gowenrw/84_Badge/art/inspiration/LSF01.jpg

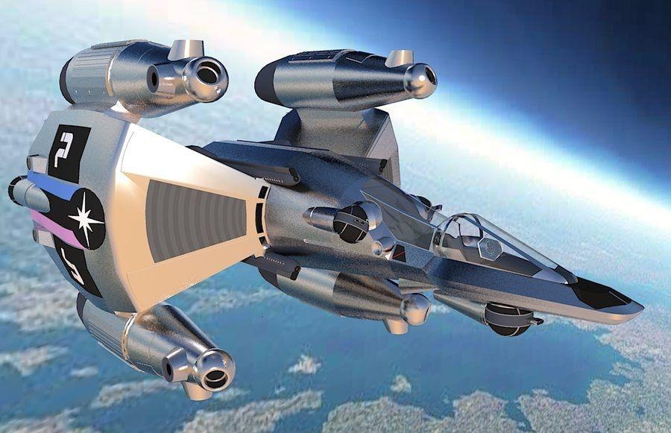
art/inspiration/LSF01.jpg
