gowenrw/84_Badge/art/inspiration/LSF02.jpg

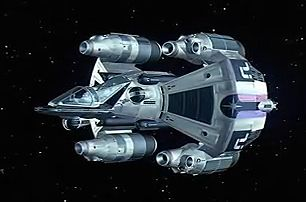
art/inspiration/LSF02.jpg
