gowenrw/84_Badge/art/inspiration/LSF03.png

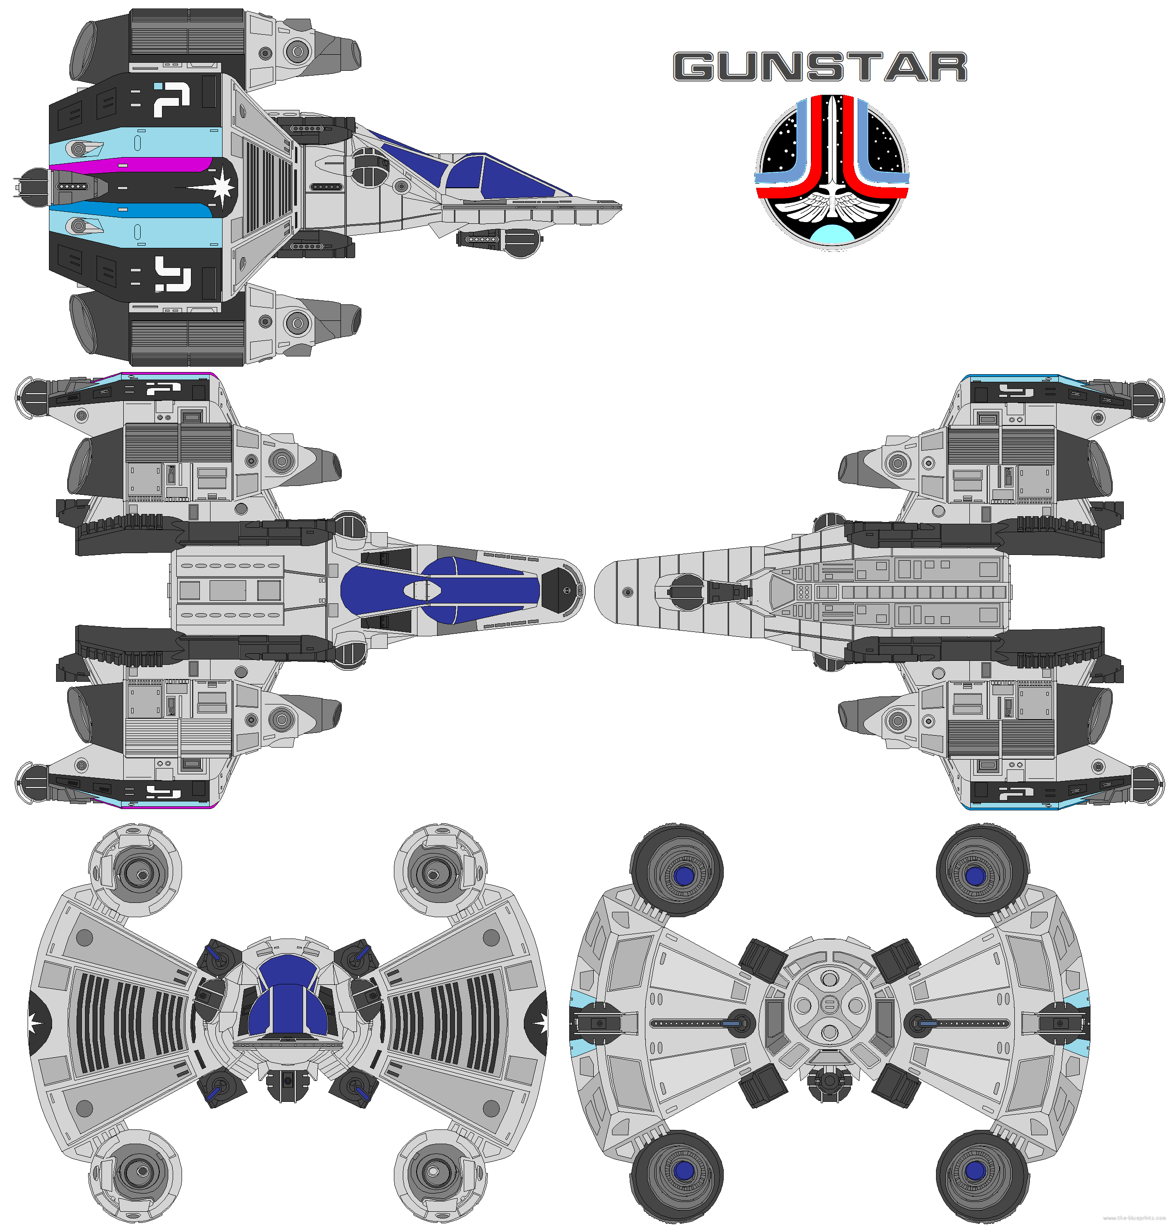
art/inspiration/LSF03.png
