gowenrw/84_Badge/art/inspiration/LSF04.jpg

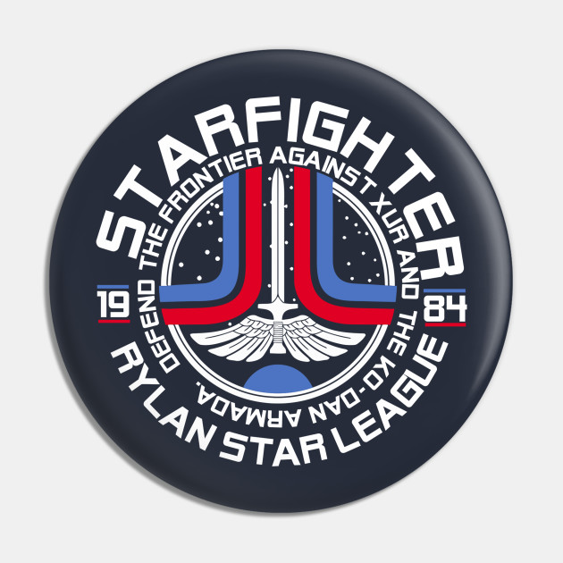
art/inspiration/LSF04.jpg
