gowenrw/84_Badge/art/inspiration/LSF05.jpg

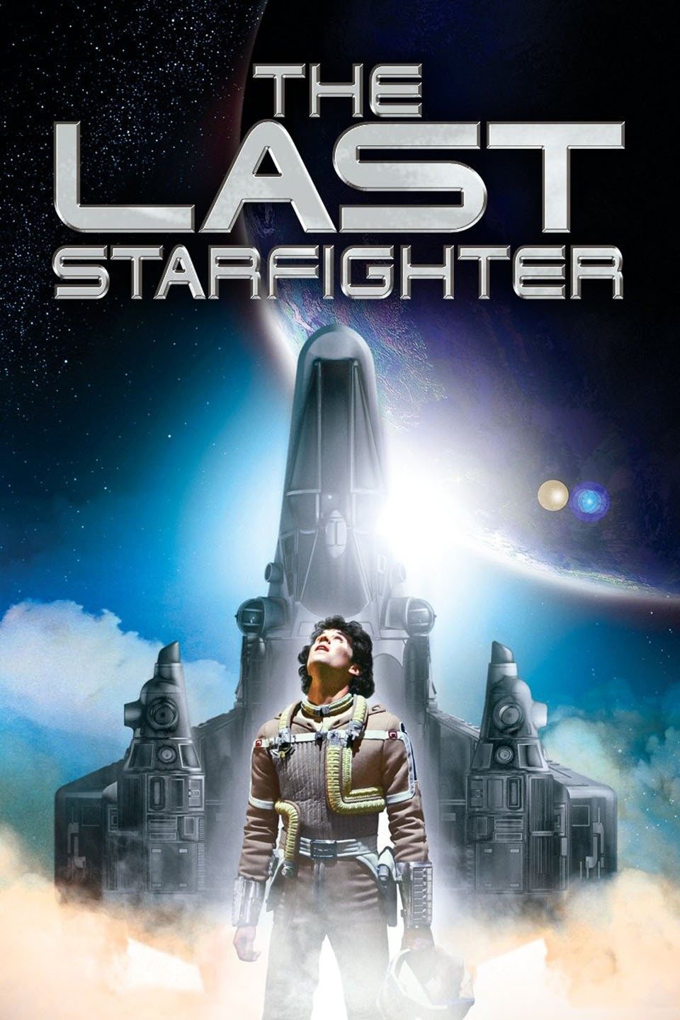
art/inspiration/LSF05.jpg
