gowenrw/84_Badge/art/inspiration/Orwell01.jpg

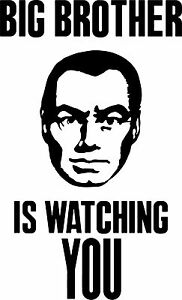
art/inspiration/Orwell01.jpg
