gowenrw/84_Badge/art/inspiration/Orwell02.jpg

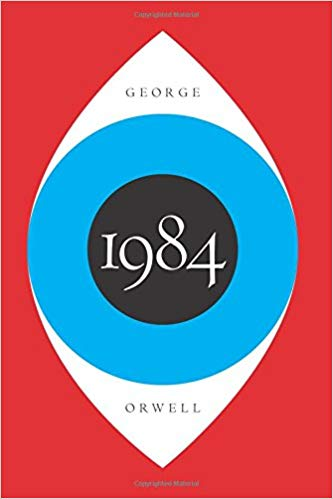
art/inspiration/Orwell02.jpg
