gowenrw/84_Badge/art/inspiration/Orwell03.jpg

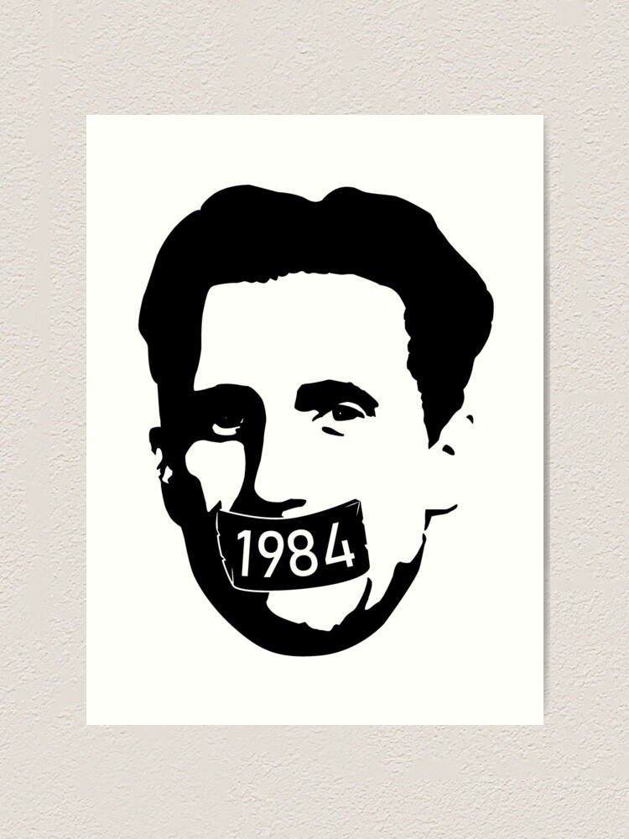
art/inspiration/Orwell03.jpg
