gowenrw/84_Badge/art/inspiration/Orwell04.png

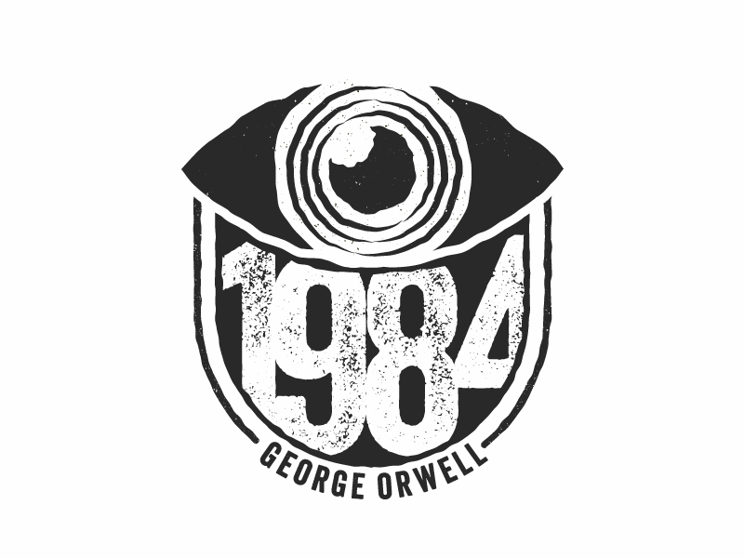
art/inspiration/Orwell04.png
