gowenrw/84_Badge/art/inspiration/Term01.jpg

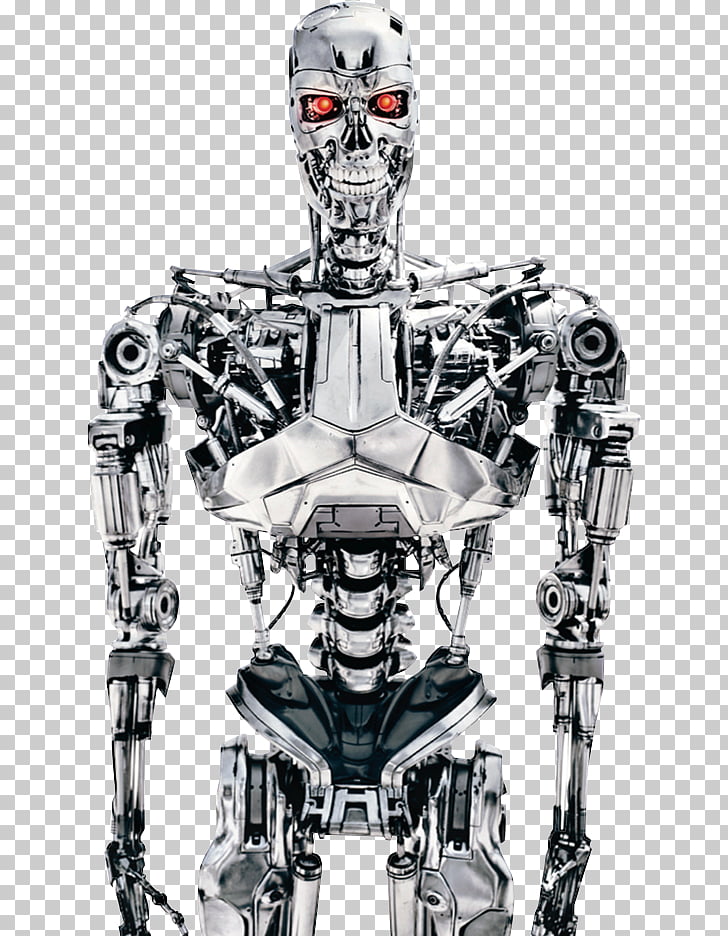
art/inspiration/Term01.jpg
