gowenrw/84_Badge/art/inspiration/Term02.jpg

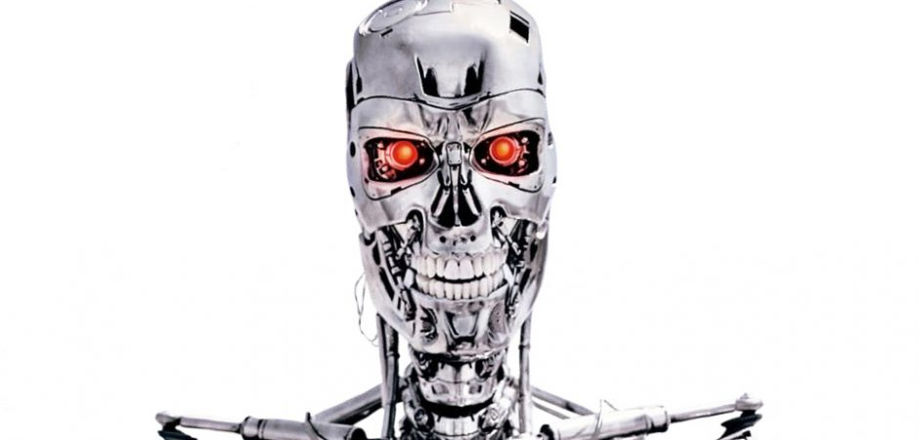
art/inspiration/Term02.jpg
