gowenrw/84_Badge/art/inspiration/Term03.jpg

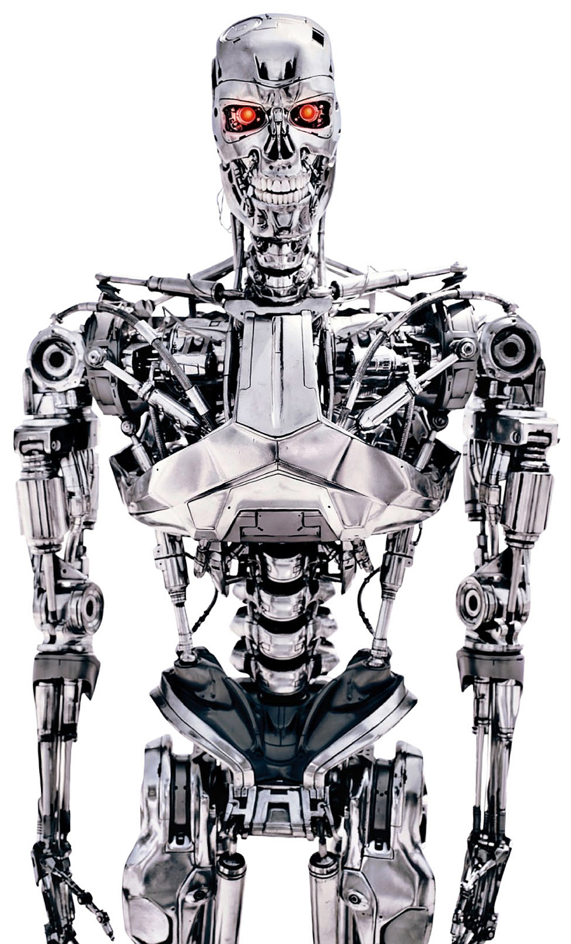
art/inspiration/Term03.jpg
