gowenrw/84_Badge/art/inspiration/Term04.jpg

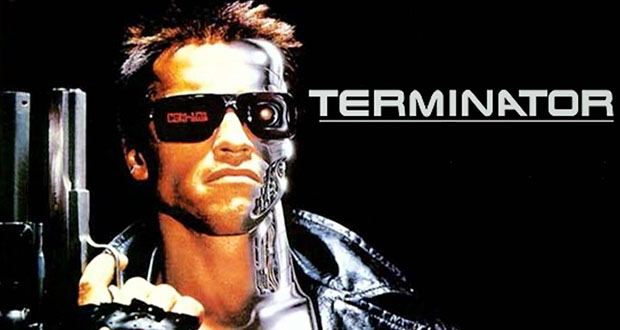
art/inspiration/Term04.jpg
