gowenrw/84_Badge/art/inspiration/Term05.jpg

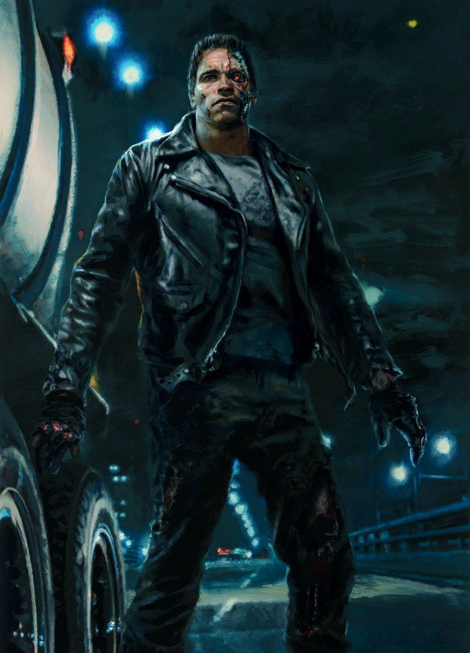
art/inspiration/Term05.jpg
