gowenrw/84_Badge/art/inspiration/WW01.jpg

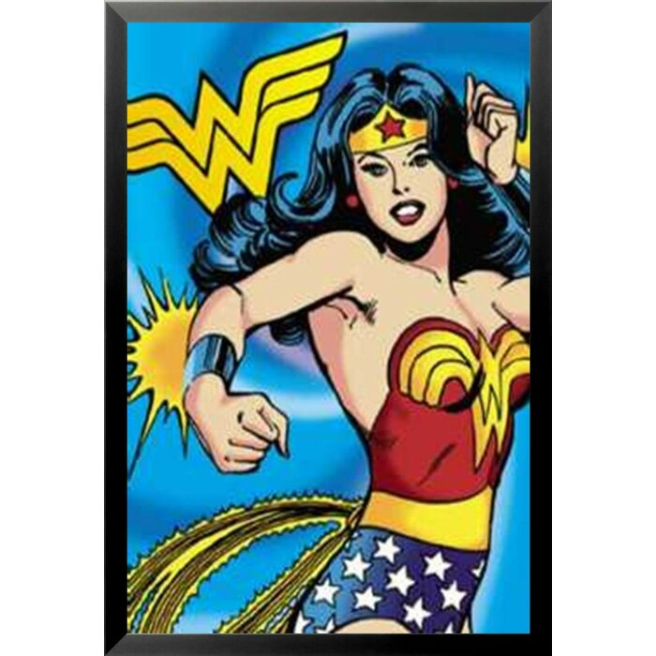
art/inspiration/WW01.jpg
