gowenrw/84_Badge/art/inspiration/WW02.jpg

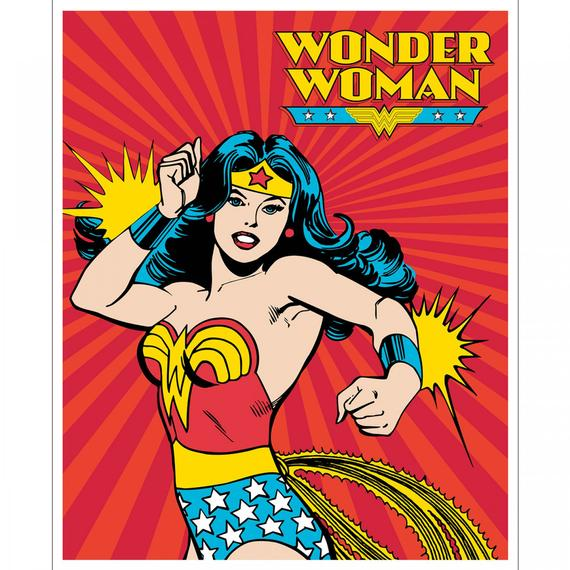
art/inspiration/WW02.jpg
