gowenrw/84_Badge/art/inspiration/WW03.jpg

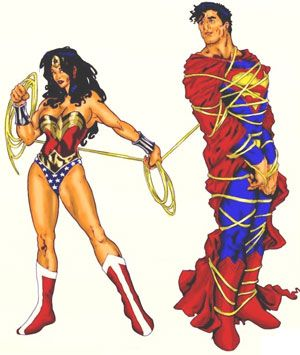
art/inspiration/WW03.jpg
