gowenrw/84_Badge/art/inspiration/WW04.jpg

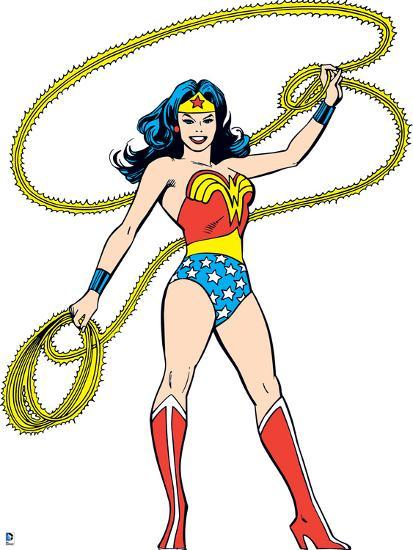
art/inspiration/WW04.jpg
