gowenrw/84_Badge/art/inspiration/WW05.jpg

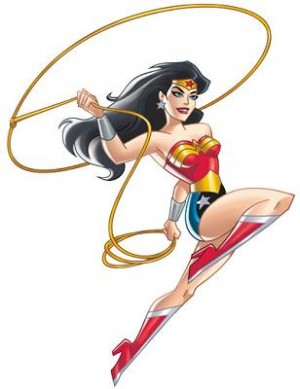
art/inspiration/WW05.jpg
