gowenrw/84_Badge/eda/prod/3d_models/TS2306A.step

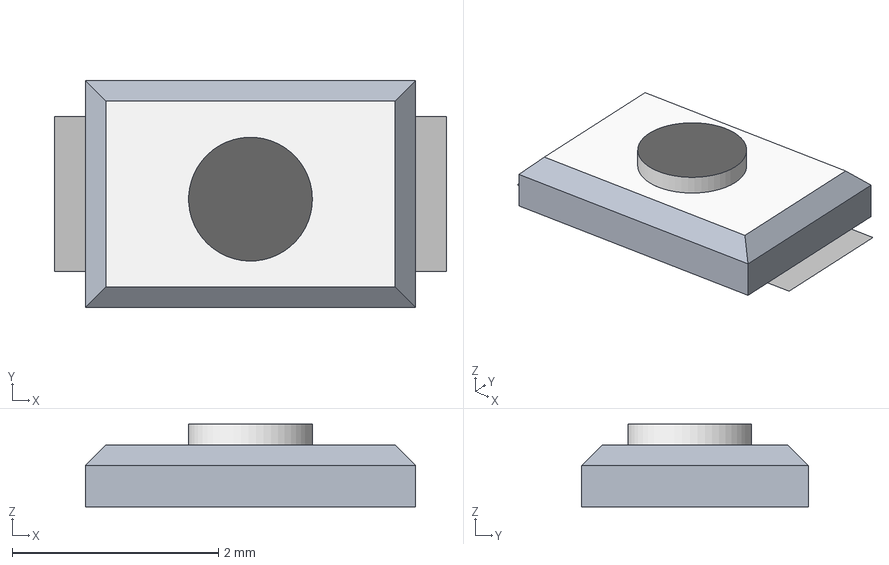
[picture p69: CAD file, 2020-01-20]
eda/prod/3d_models/TS2306A.step
3.80 x 2.20 x 0.8 mm
Plane
