gowenrw/84_Badge/eda/dev/3d_models/C_1206_3216Metric.step

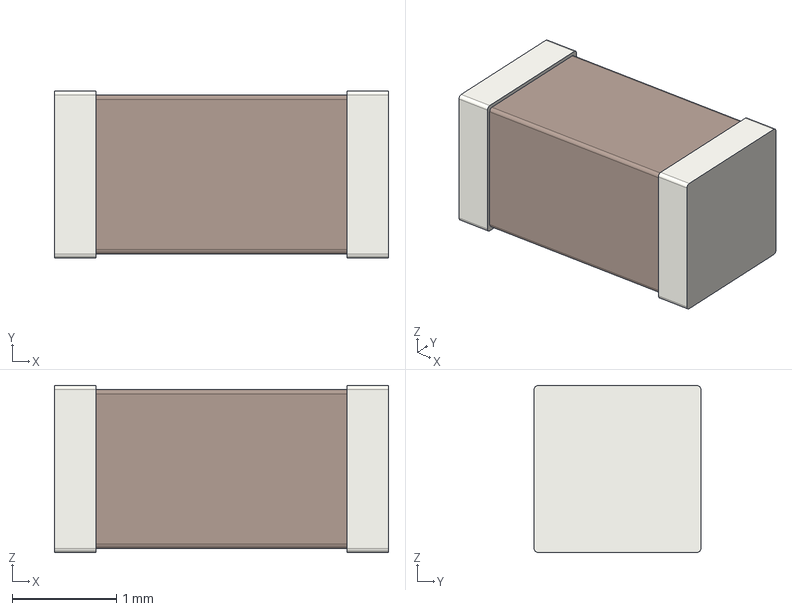
[picture p70: CAD file, 2020-01-20]
eda/dev/3d_models/C_1206_3216Metric.step
3.20 x 1.60 x 1.60 mm
