gowenrw/84_Badge/eda/prod/3d_models/RJ45_Amphenol_RJHSE-5080-56544.STEP

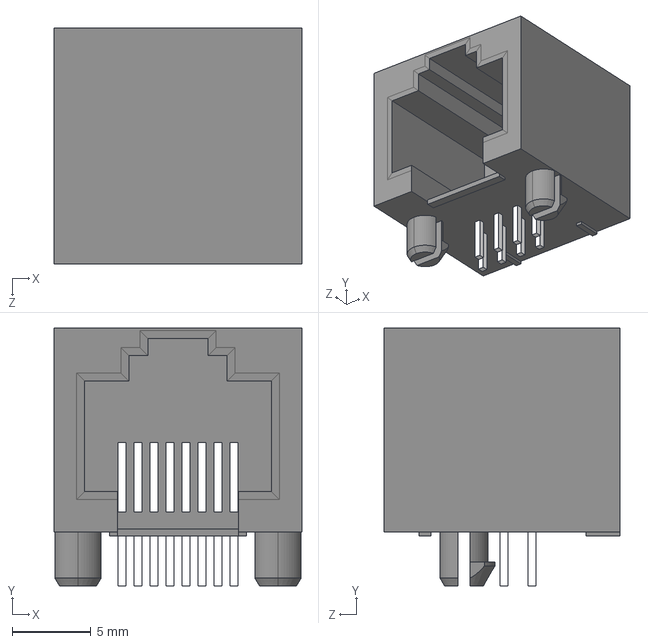
[picture p71: CAD file, 2020-01-20]
eda/prod/3d_models/RJ45_Amphenol_RJHSE-5080-56544.STEP
15.7 x 16.4 x 15.0 mm
