gowenrw/84_Badge/eda/prod/3d_models/PinHeader_1x08_P2.54mm_Vertical.step

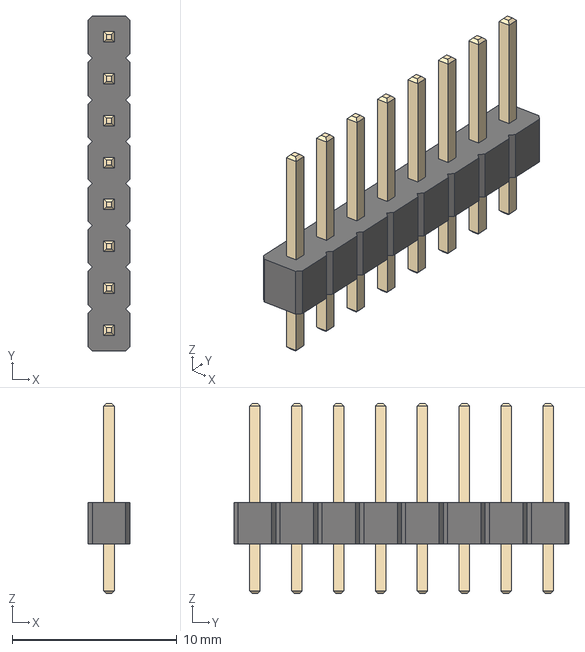
[picture p73: CAD file, 2020-01-20]
eda/prod/3d_models/PinHeader_1x08_P2.54mm_Vertical.step
2.54 x 20.3 x 11.5 mm
