gowenrw/84_Badge/eda/prod/3d_models/C_Disc_D3.0mm_W2.0mm_P2.50mm.step

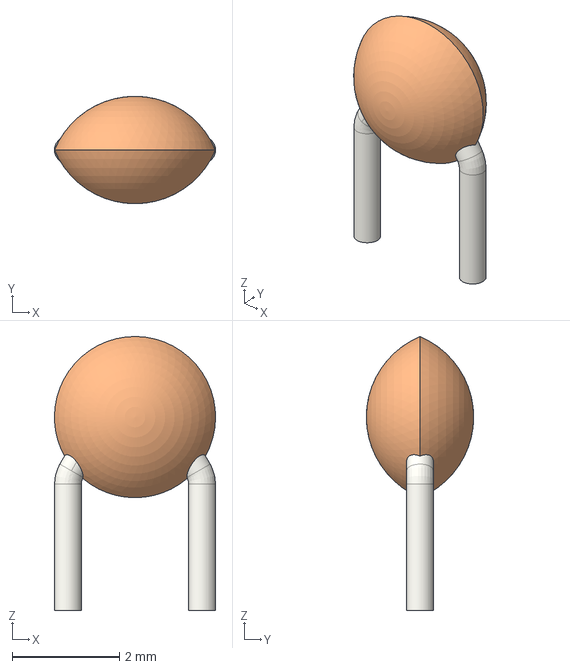
[picture p74: CAD file, 2020-01-20]
eda/prod/3d_models/C_Disc_D3.0mm_W2.0mm_P2.50mm.step
3.00 x 2.00 x 5.10 mm
