gowenrw/84_Badge/eda/prod/3d_models/R_0805_2012Metric.step

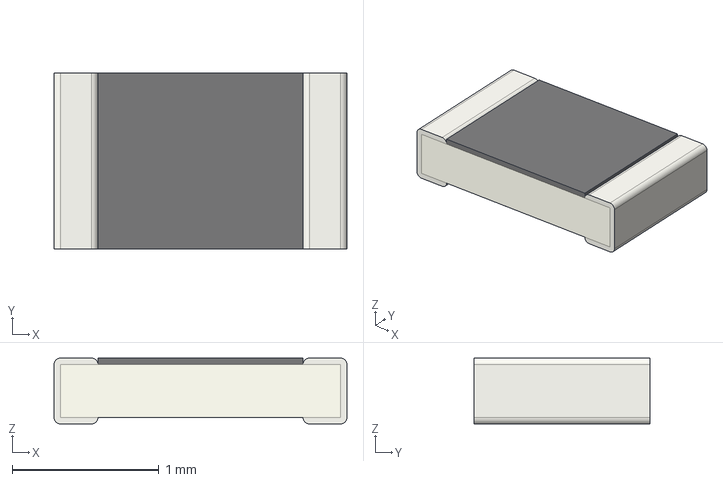
[picture p75: CAD file, 2020-01-20]
eda/prod/3d_models/R_0805_2012Metric.step
2.00 x 1.20 x 0.45 mm
