gowenrw/84_Badge/eda/dev/3d_models/RJ45_Amphenol_RJHSE538X.step

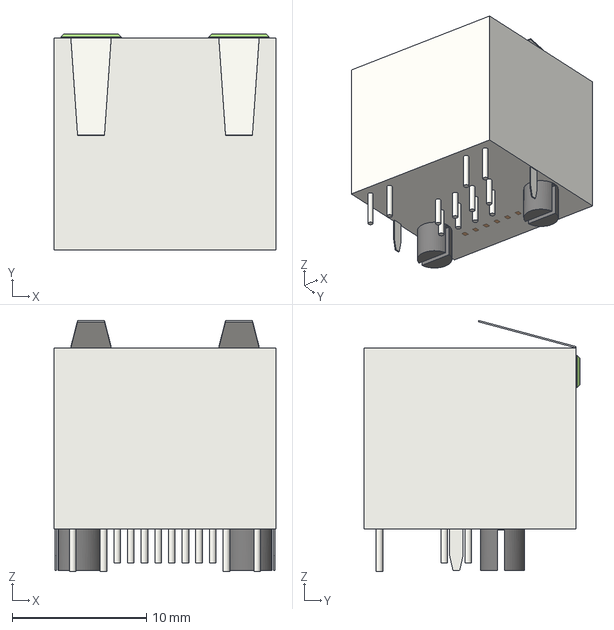
[picture p76: CAD file, 2020-01-20]
eda/dev/3d_models/RJ45_Amphenol_RJHSE538X.step
16.5 x 16.1 x 18.7 mm
