gowenrw/84_Badge/eda/prod/3d_models/USB_Micro-B_Molex_47346-0001.step

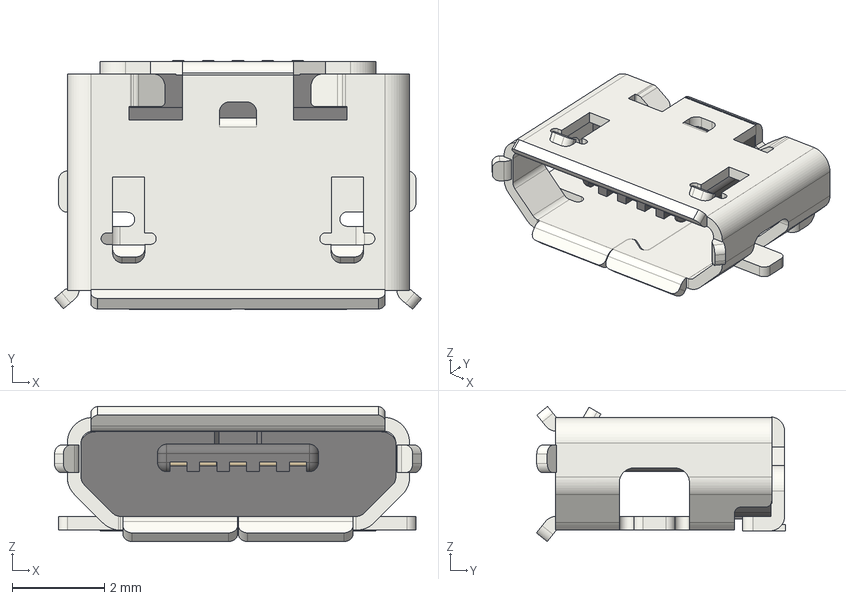
[picture p77: CAD file, 2020-01-20]
eda/prod/3d_models/USB_Micro-B_Molex_47346-0001.step
7.98 x 5.42 x 2.94 mm
