gowenrw/84_Badge/eda/prod/3d_models/SW_SPDT_PCM12.step

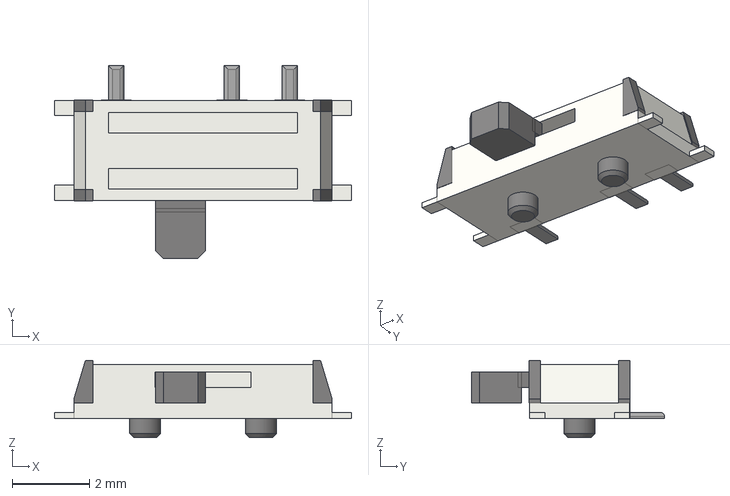
[picture p79: CAD file, 2020-01-20]
eda/prod/3d_models/SW_SPDT_PCM12.step
7.70 x 5.00 x 2.00 mm
