gowenrw/84_Badge/eda/dev/3d_models/C_0805_2012Metric.step

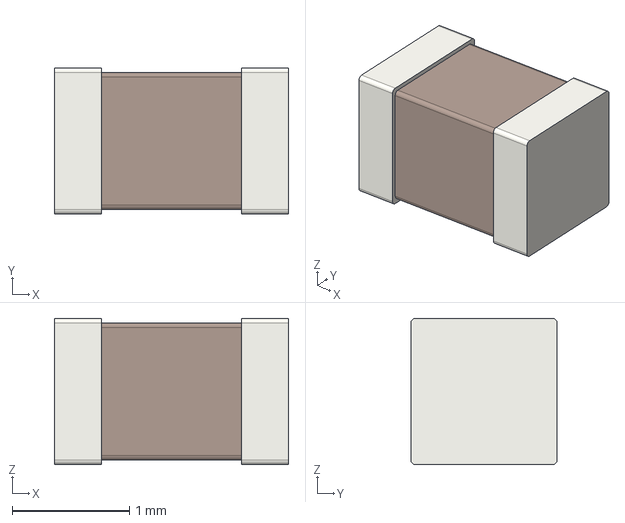
[picture p80: CAD file, 2020-01-20]
eda/dev/3d_models/C_0805_2012Metric.step
2.00 x 1.25 x 1.25 mm
