gowenrw/84_Badge/eda/prod/3d_models/SW_PUSH_6mm.step

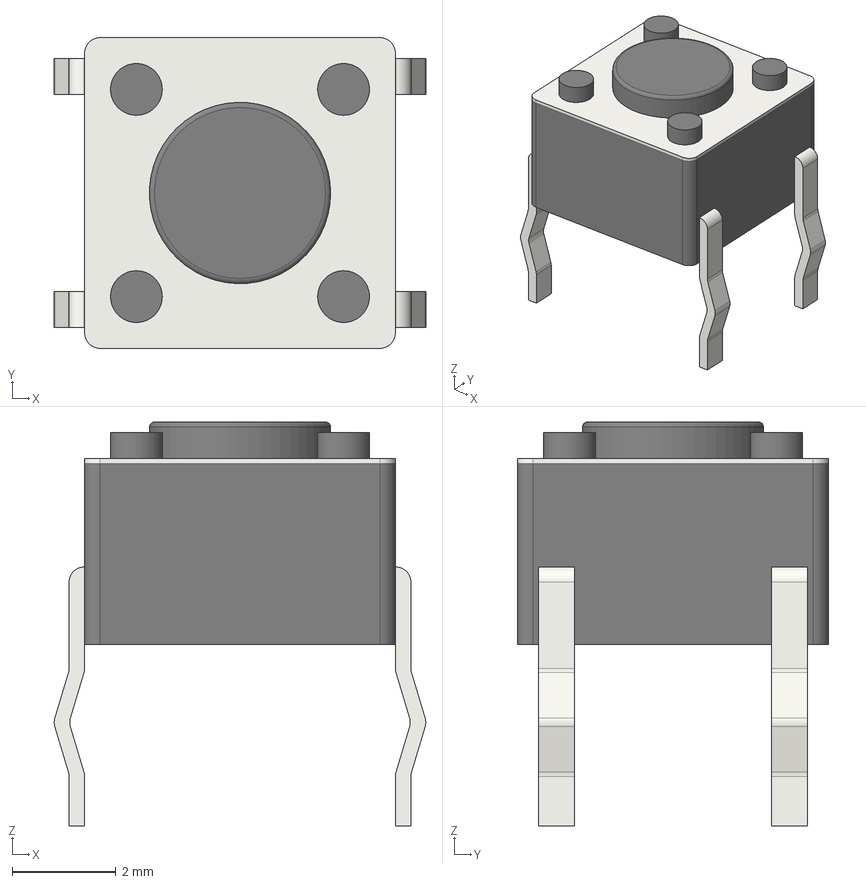
[picture p81: CAD file, 2020-01-20]
eda/prod/3d_models/SW_PUSH_6mm.step
7.17 x 6.00 x 7.80 mm
