gowenrw/84_Badge/eda/dev/3d_models/Battery_Holder_3xAAA_Simple.step

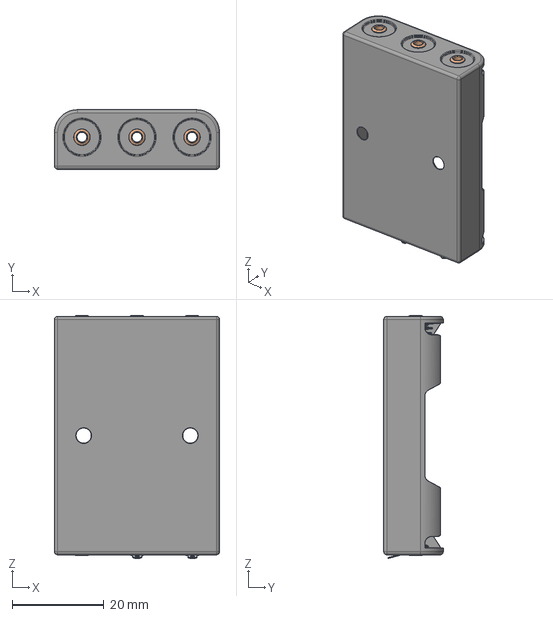
[picture p82: CAD file, 2020-01-20]
eda/dev/3d_models/Battery_Holder_3xAAA_Simple.step
36.0 x 13.0 x 53.0 mm
