gowenrw/84_Badge/eda/dev/3d_models/R_1206_3216Metric.step

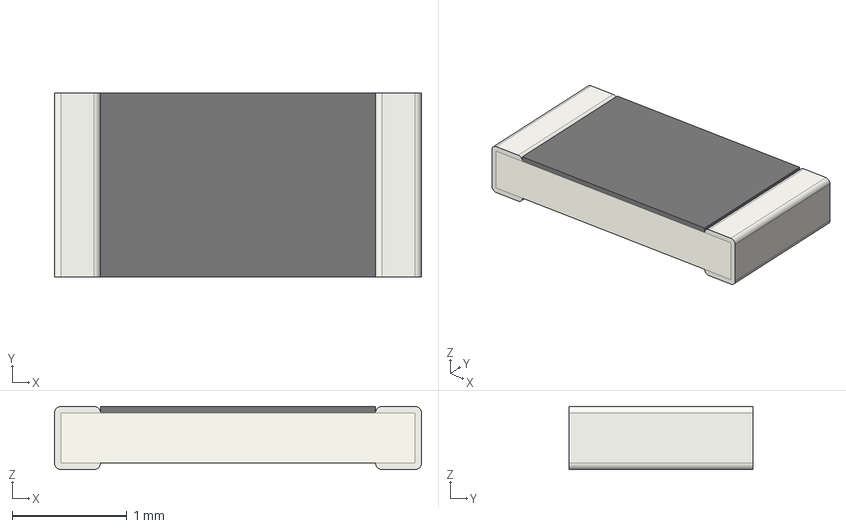
[picture p84: CAD file, 2020-01-20]
eda/dev/3d_models/R_1206_3216Metric.step
3.20 x 1.60 x 0.55 mm
