gowenrw/84_Badge/eda/prod/3d_models/PinHeader_1x02_P2.54mm_Vertical.step

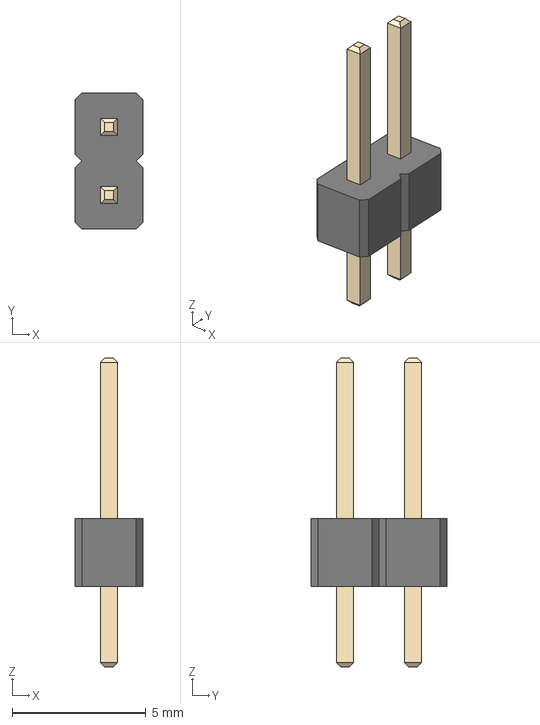
[picture p85: CAD file, 2020-01-20]
eda/prod/3d_models/PinHeader_1x02_P2.54mm_Vertical.step
2.54 x 5.08 x 11.5 mm
